PataZik/TIme-Cortex-Diplomarbeit/themenstellungen/diplomarbeit_gesamt.adoc

:doctype: book
:toc: macro
:source-highlighter: rouge
:icons: font
// Lade die entsprechende Kopfzeile (kopfzeile_diplomarbeit_aul, ..._hif oder ..._kolleg)
:header_image: kopfzeile_diplomarbeit_aul.png
:pdf-page-size: a4
:toc-title: Inhaltsverzeichnis
:lang: DE
:hyphens:

// Lädt das PDF, das aus der Wordvorlage erzeugt wurde, zu Beginn der Arbeit.
// 

// Schreibt das Inhaltsverzeichnis
toc::[]

// Füge die Arbeit jedes einzelnen ein.
// WICHTIG: Nach jedem include muss eine Leerzeile sein!

include::diplomarbeit_alzo.adoc[]

include::diplomarbeit_dekoo.adoc[]

// include::diplomarbeit_themenstellung_nachname2.adoc[]

// include::diplomarbeit_themenstellung_nachname3.adoc[]

// include::diplomarbeit_themenstellung_nachname4.adoc[]

// Hier kannst du ggf. Anhänge aus externen Quellen laden.
//
