PataZik/TIme-Cortex-Diplomarbeit/Platine - deKoo/prompt_inhalt.md

Ich benötige ein Inhaltsverzeichnis für eine vorwissenschaftliche Arbeit.

## Inhalt

Meine individuelle Themenstellung ist

Eine funktionsfähige, getestete Platine mit RFID-Lesegerät, die Mitarbeiterchips fehlerfrei erkennt und die Daten an die nachfolgenden Systeme weitergibt. Das Modul bildet die Grundlage für die gesamte Zeiterfassung.

Das Untersuchungsanliegen ist wie folgt:

Auswahl und Testung verschiedener Mikrocontroller und weiterer Bauteile. Planung und Erstellung einer eigenen Platine sowie Zusammenbau aller Komponenten. Sicherstellung der Funktionsfähigkeit und Effizienz des Gesamtsystems.

## Quellen

(Gib hier die Ordner und die Beschreibung an, was sie beinhalten)

## Regeln für die Ausgabe

Gib das Inhaltsverzeichnis als nicht numerierte Liste in einem Codefenster zum Kopieren aus.

## Abgrenzung

Das Projektmanagement ist NICHT Teil dieser Arbeit.
